ak66666/ThumbsUpV5MXProMicro/Photos/IMG_20230603_192714543.jpg

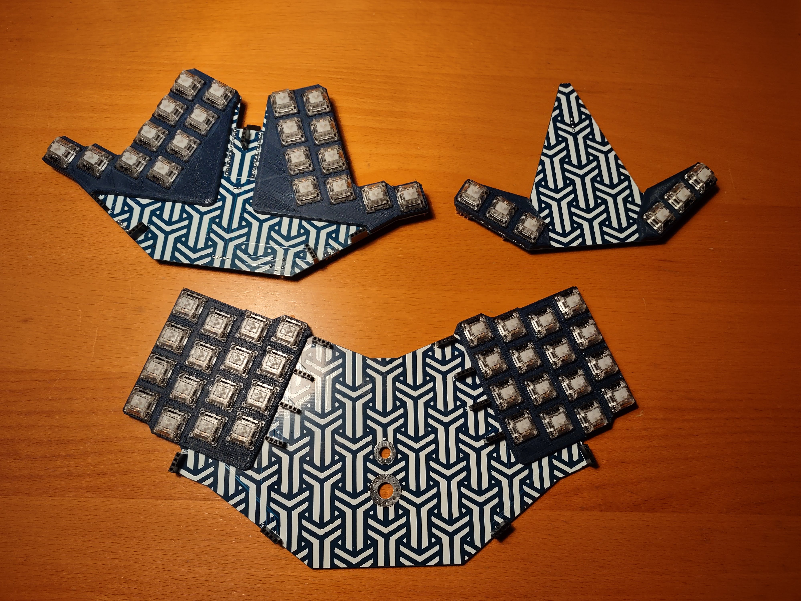
Photos/IMG_20230603_192714543.jpg
