ak66666/ThumbsUpV5MXProMicro/Photos/IMG_20230603_193150938.jpg

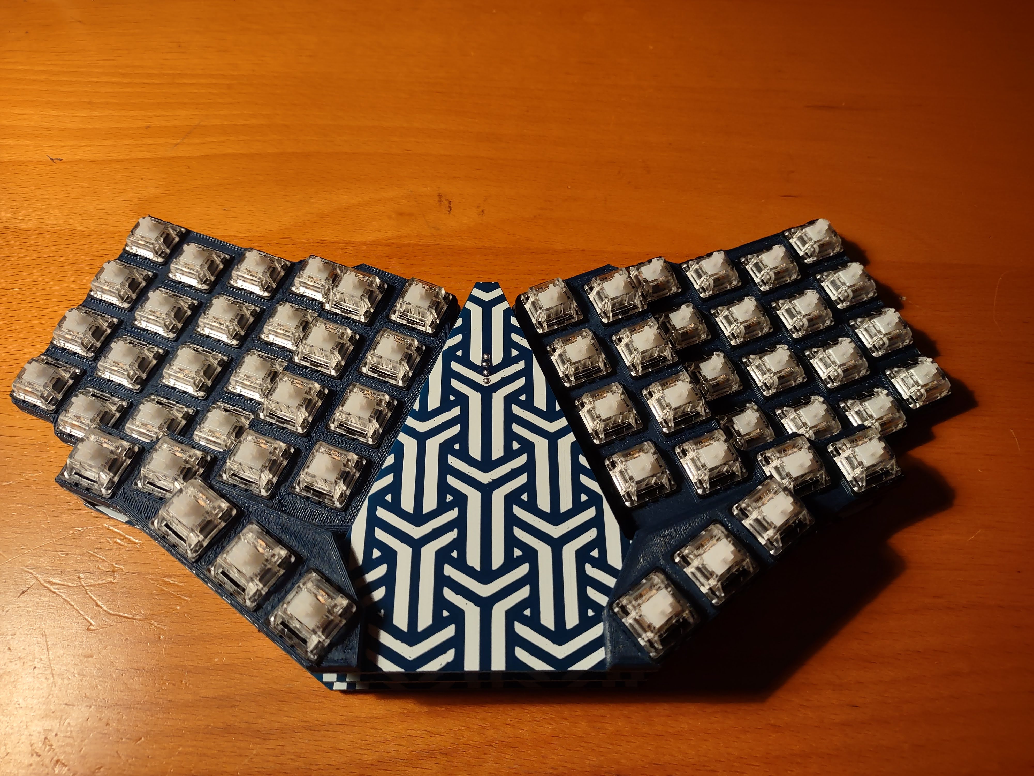
Photos/IMG_20230603_193150938.jpg
