ak66666/ThumbsUpV5MXProMicro/Photos/IMG_20230603_193208370.jpg

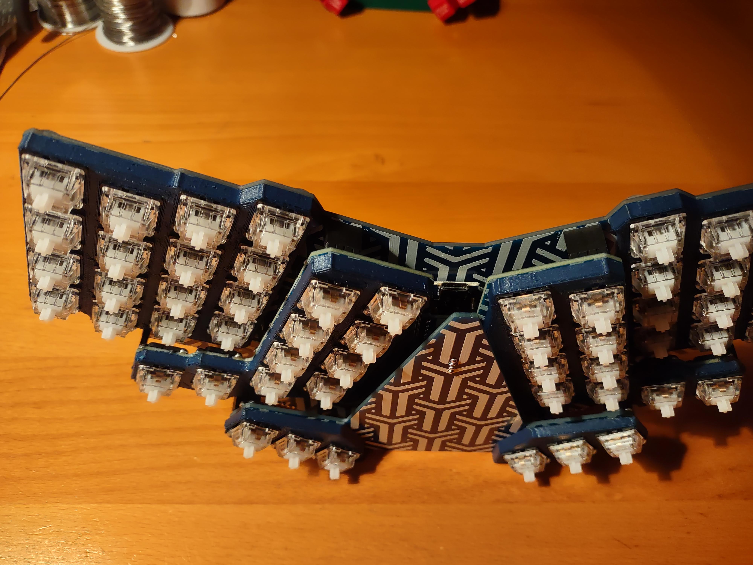
Photos/IMG_20230603_193208370.jpg
