ak66666/ThumbsUpV5MXProMicro/Photos/IMG_20230603_193236321_HDR.jpg

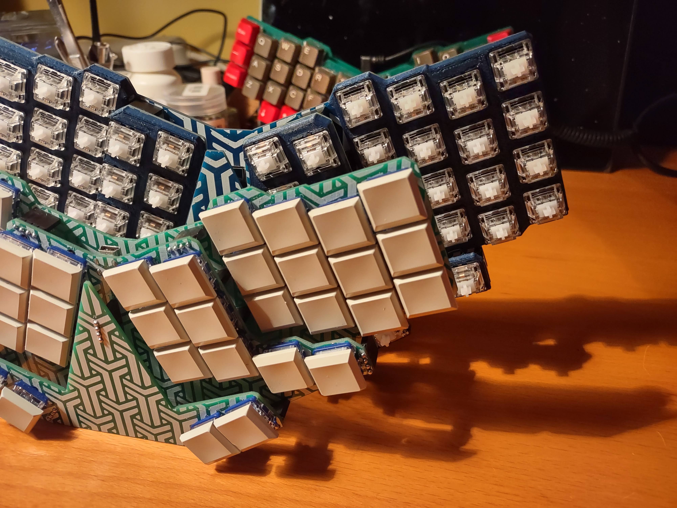
Photos/IMG_20230603_193236321_HDR.jpg
