ak66666/ThumbsUpV5MXProMicro/Photos/IMG_20230603_193300118.jpg

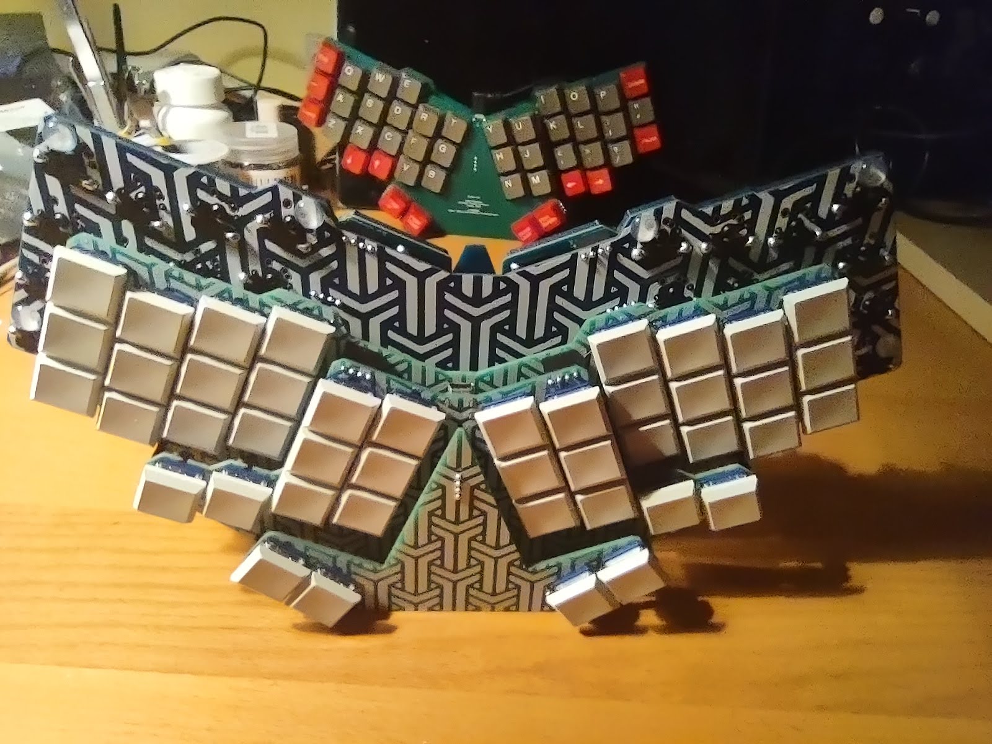
Photos/IMG_20230603_193300118.jpg
