ak66666/ThumbsUpV5MXProMicro/Photos/IMG_20230603_194638332_HDR.jpg

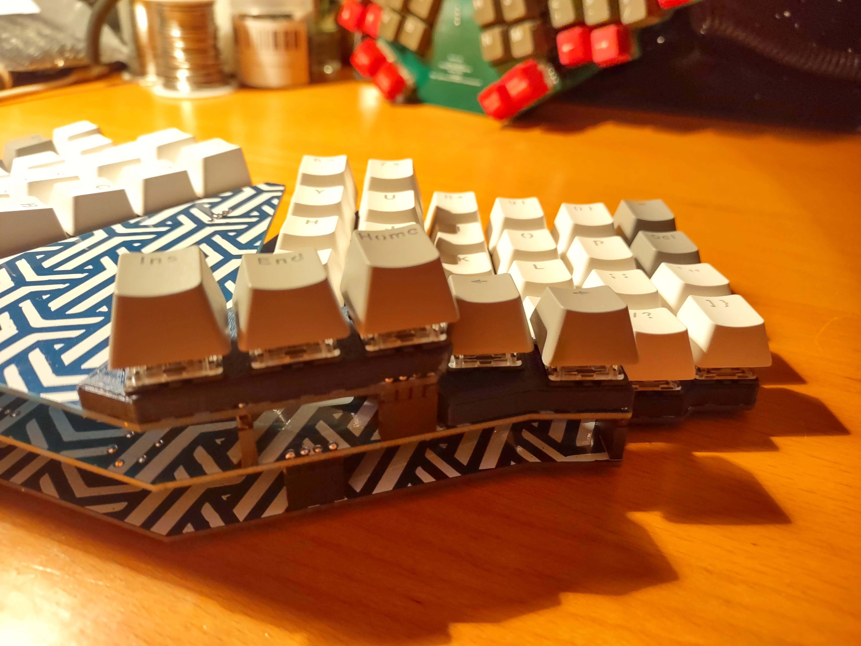
Photos/IMG_20230603_194638332_HDR.jpg
