ak66666/ThumbsUpV5MXProMicro/Photos/IMG_20230603_194709066.jpg

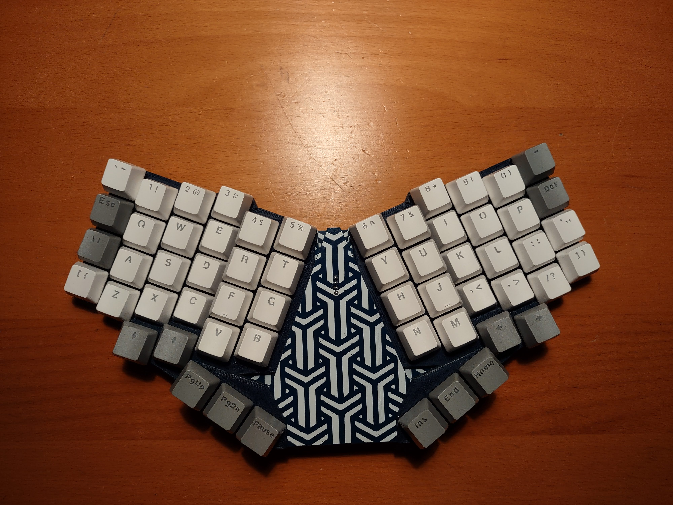
Photos/IMG_20230603_194709066.jpg
