ak66666/ThumbsUpV5MXProMicro/Photos/IMG_20230603_194831133.jpg

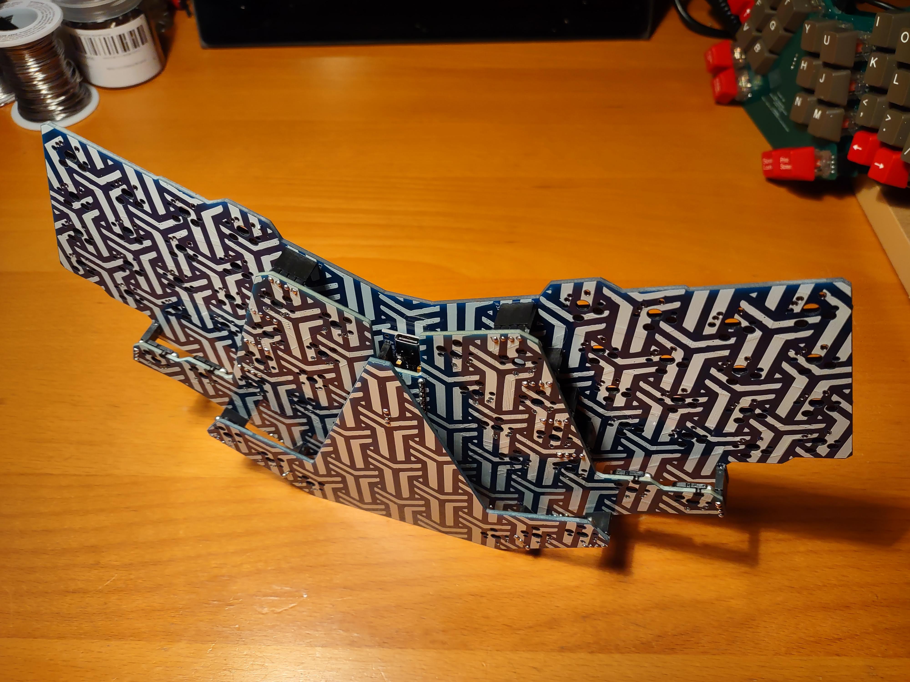
Photos/IMG_20230603_194831133.jpg
