ak66666/ThumbsUpV5MXProMicro/Photos/IMG_20230603_194852590.jpg

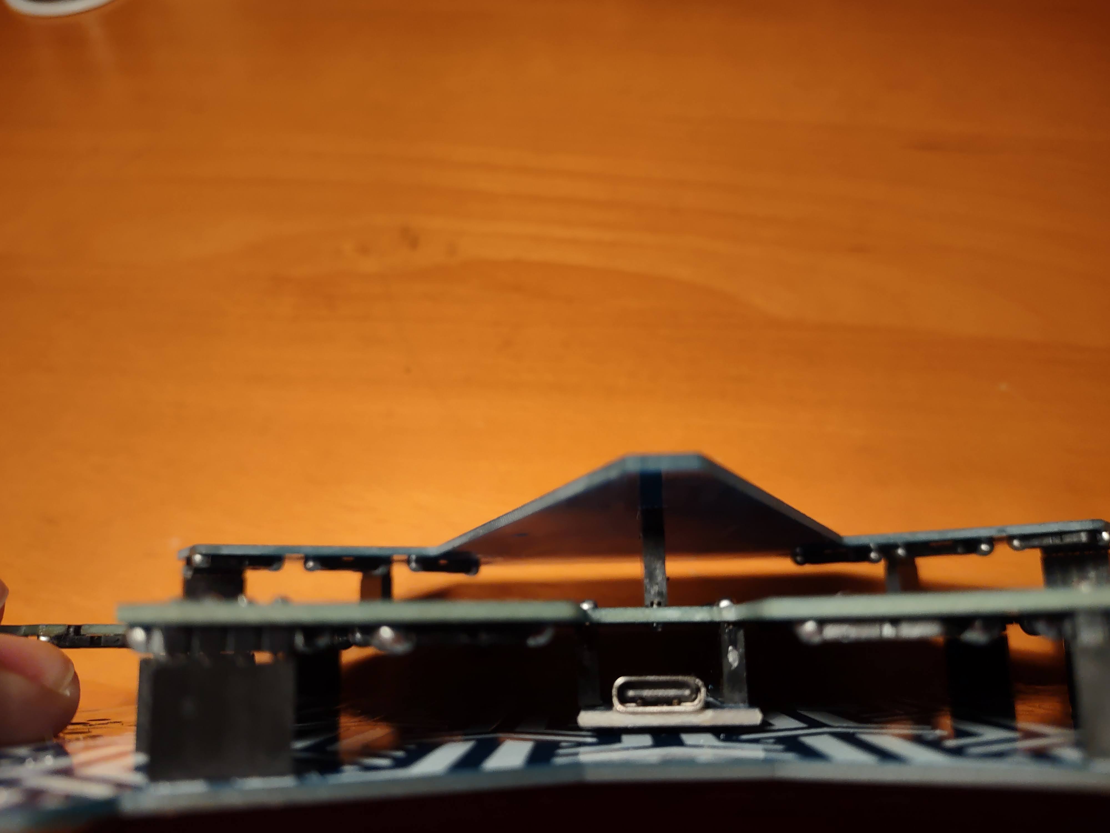
Photos/IMG_20230603_194852590.jpg
