ak66666/ThumbsUpV5MXProMicro/Photos/IMG_20230603_194928451_HDR.jpg

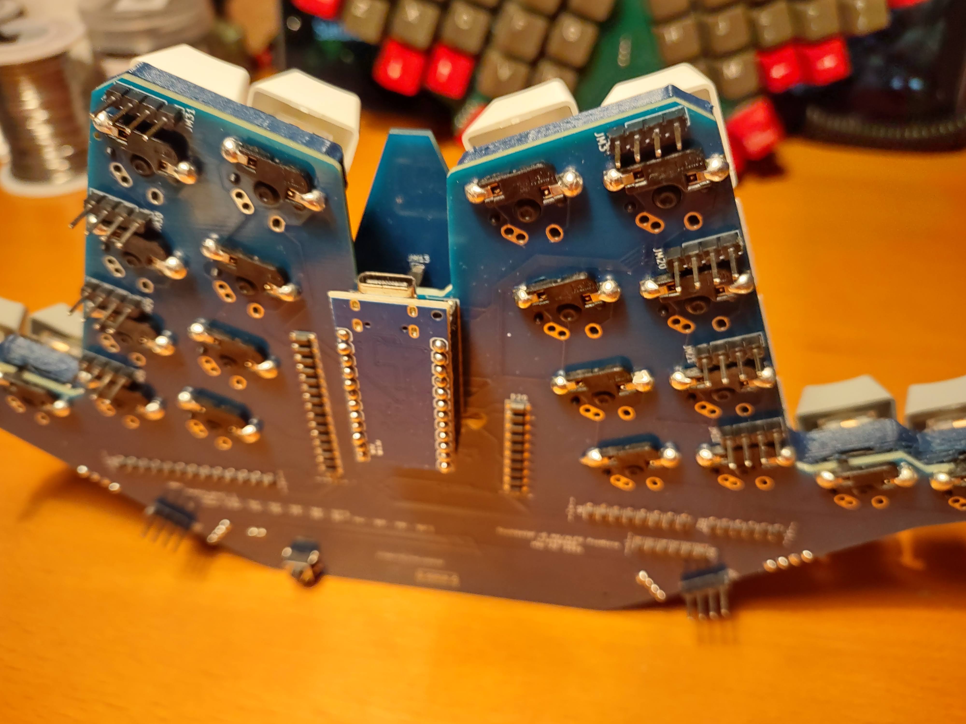
Photos/IMG_20230603_194928451_HDR.jpg
