ak66666/ThumbsUpV5MXProMicro/Photos/IMG_20230605_135358066_HDR.jpg

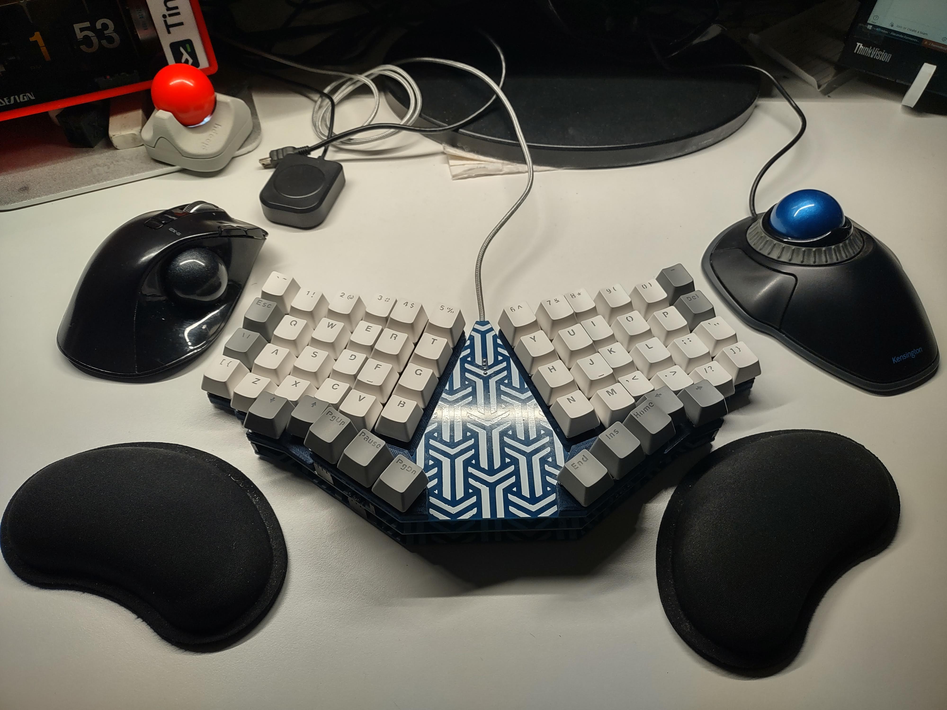
Photos/IMG_20230605_135358066_HDR.jpg
