ak66666/ThumbsUpV5MXProMicro/Photos/IMG_20230608_082447572.jpg

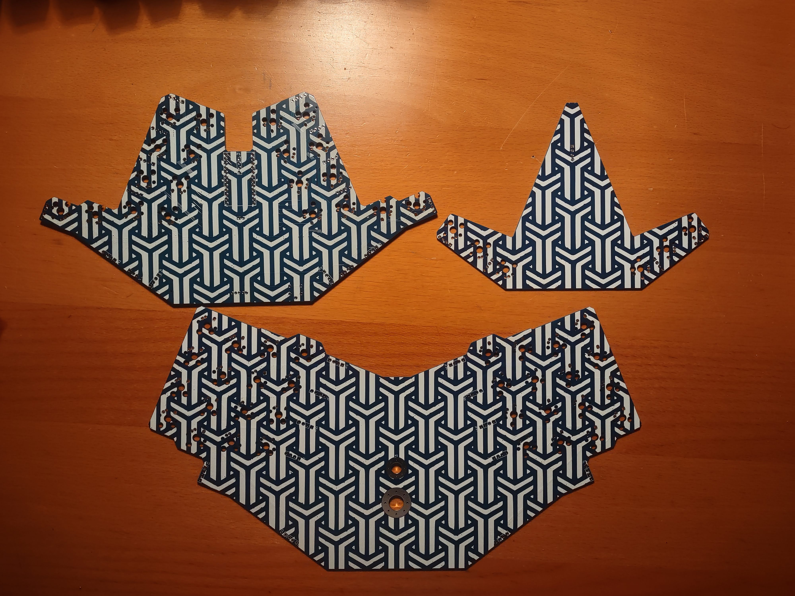
Photos/IMG_20230608_082447572.jpg
