ak66666/ThumbsUpV5MXProMicro/Photos/IMG_20230608_082502617.jpg

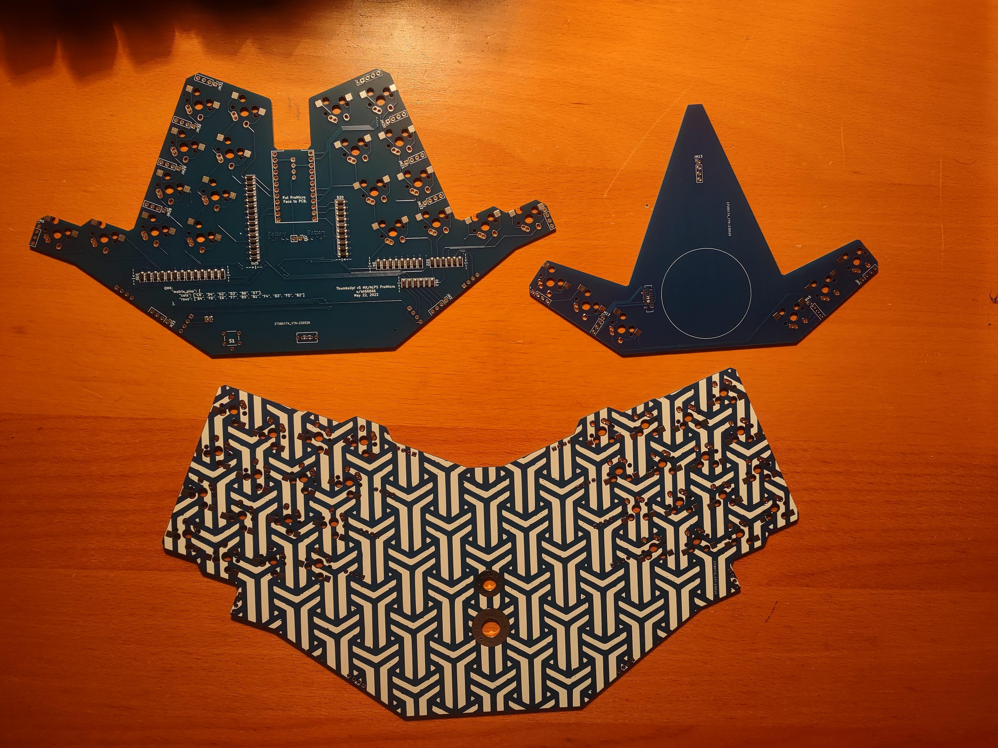
Photos/IMG_20230608_082502617.jpg
