ak66666/ThumbsUpV5MXProMicro/Photos/IMG_20230608_092843902.jpg

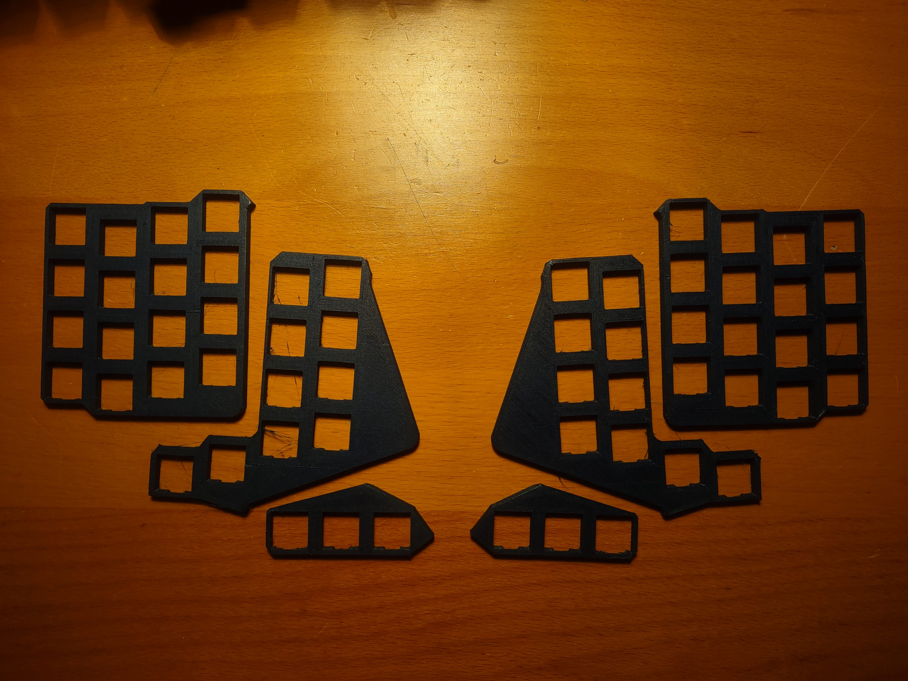
Photos/IMG_20230608_092843902.jpg
