ak66666/ThumbsUpV5MXProMicro/Silkscreens/44 Key Keyboard Layout 20 pct.png

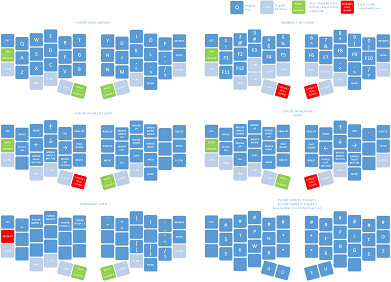
Silkscreens/44 Key Keyboard Layout 20 pct.png
