ak66666/ThumbsUpV5MXProMicro/Silkscreens/Pattern.png

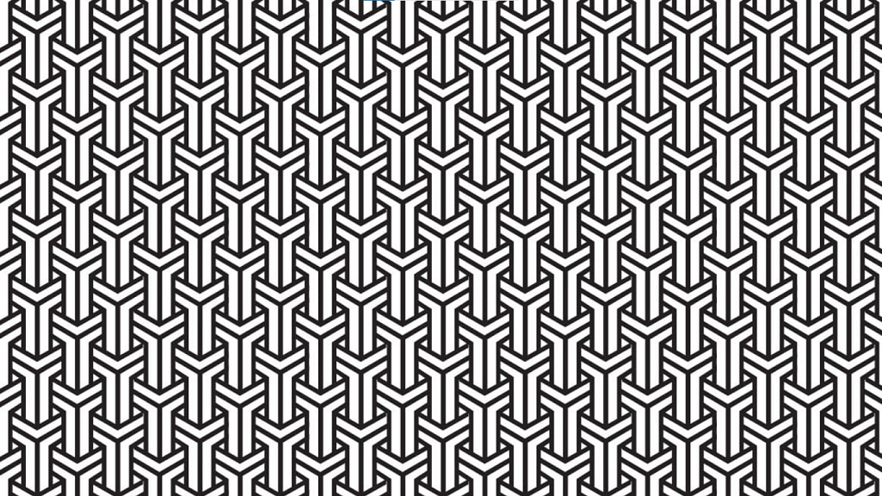
Silkscreens/Pattern.png
