ak66666/ThumbsUpV5MXProMicro/Silkscreens/QWERTY.png

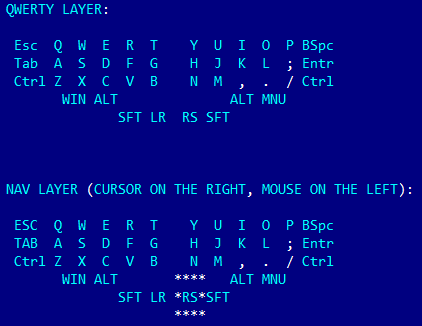
Silkscreens/QWERTY.png
